rishivg/IO-SDR/Images/1.png

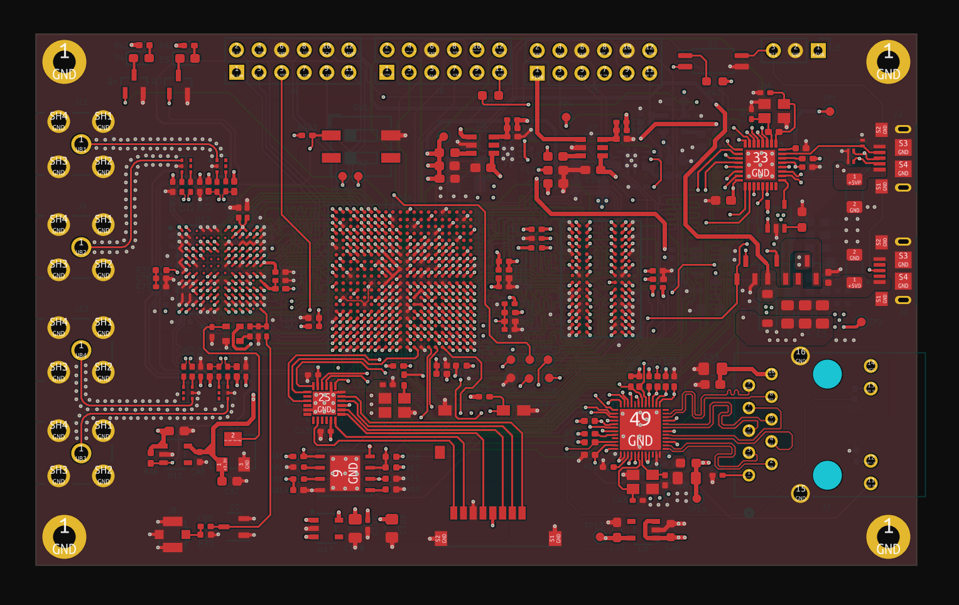
Images/1.png
