rishivg/IO-SDR/Images/2.png

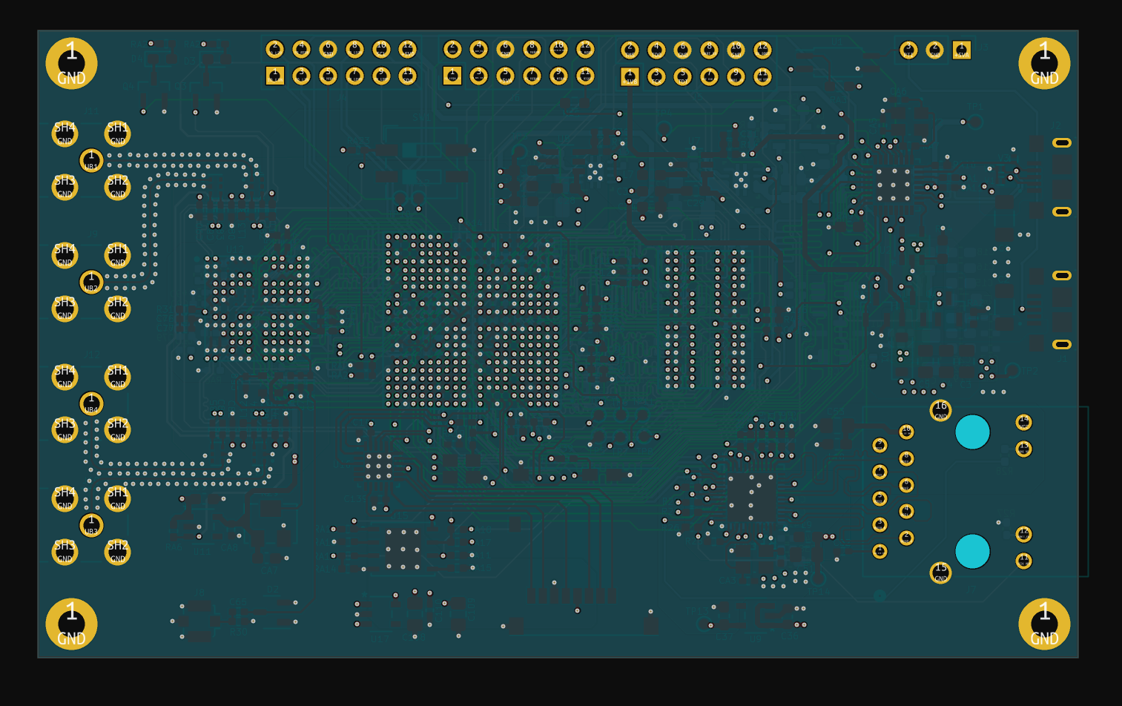
Images/2.png
