rishivg/IO-SDR/Images/3.png

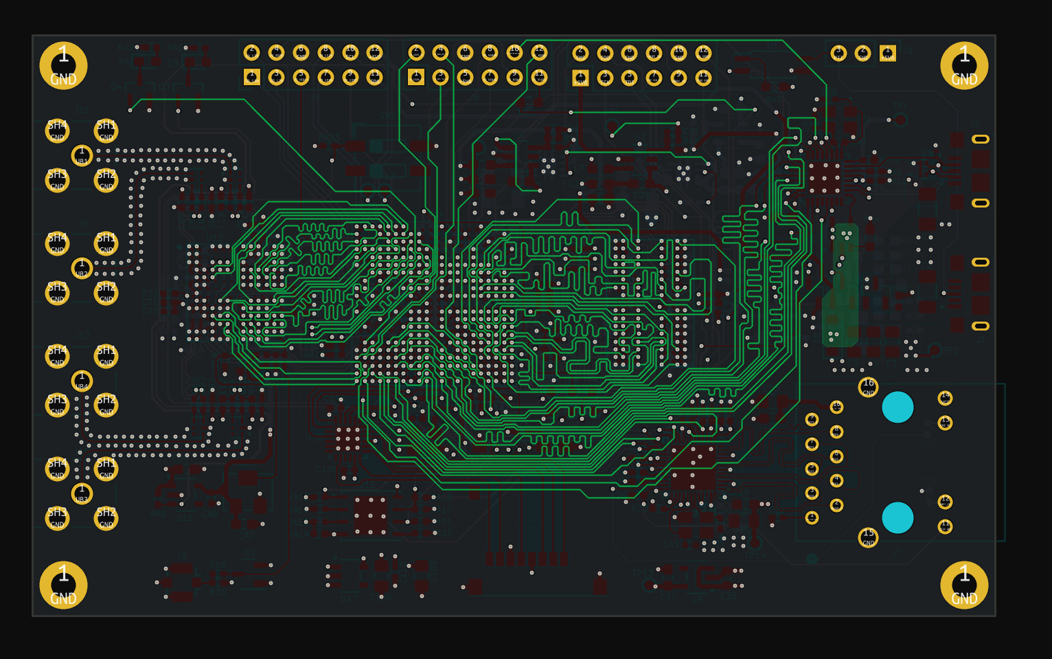
Images/3.png
