rishivg/IO-SDR/Images/4.png

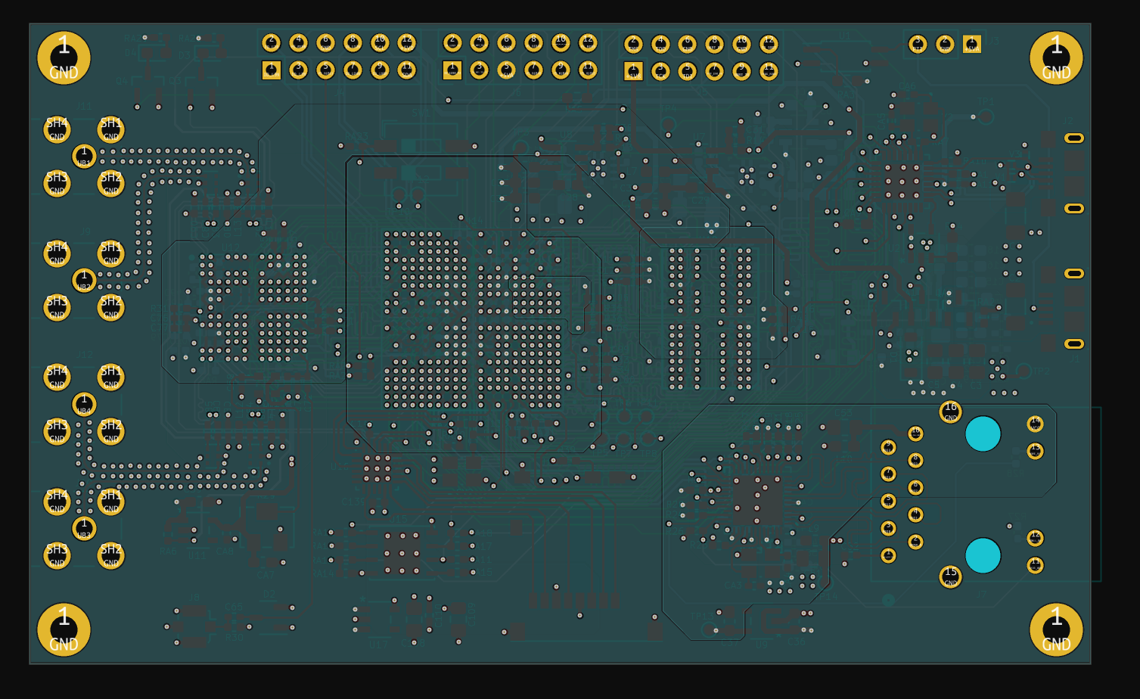
Images/4.png
