rishivg/IO-SDR/Images/5.png

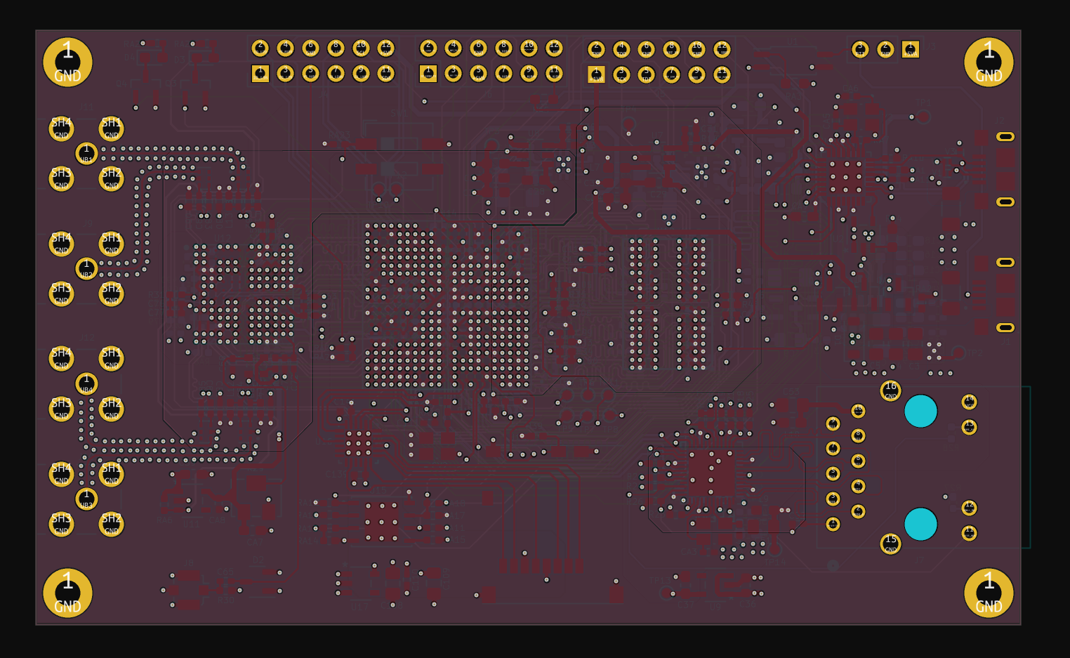
Images/5.png
