rishivg/IO-SDR/Images/6.png

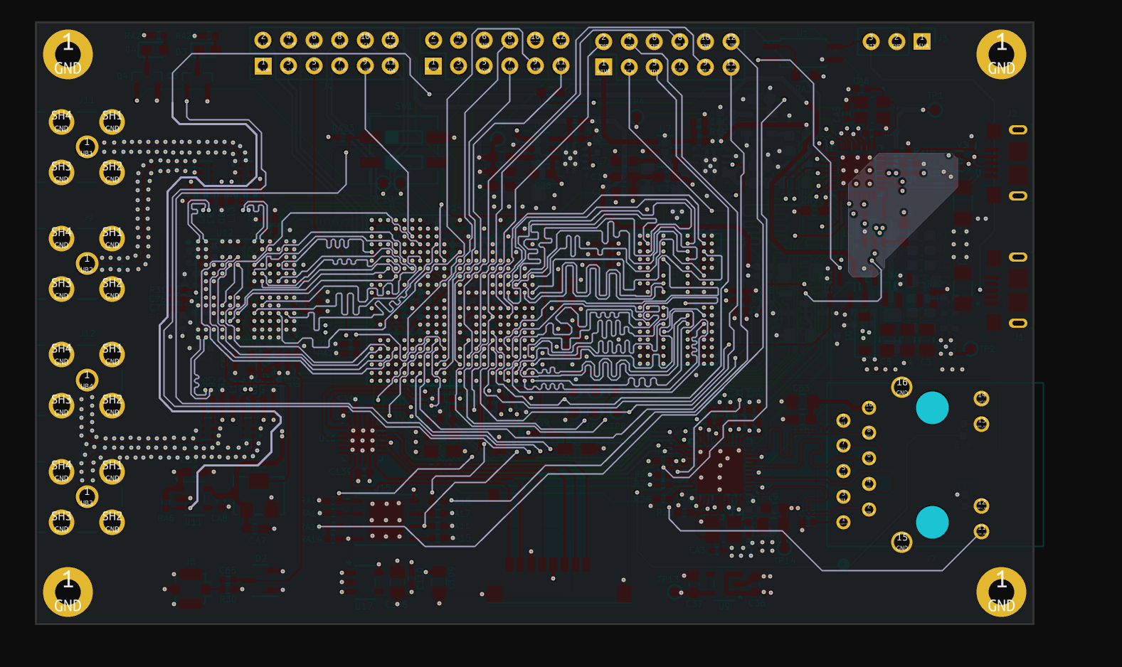
Images/6.png
