rishivg/IO-SDR/Images/7.png

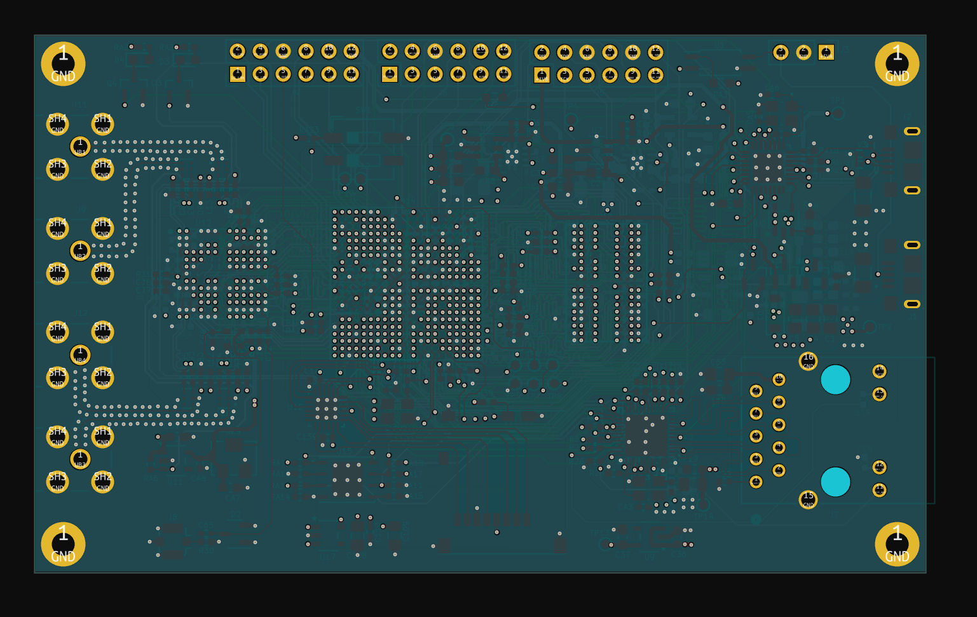
Images/7.png
