rishivg/IO-SDR/Images/8.png

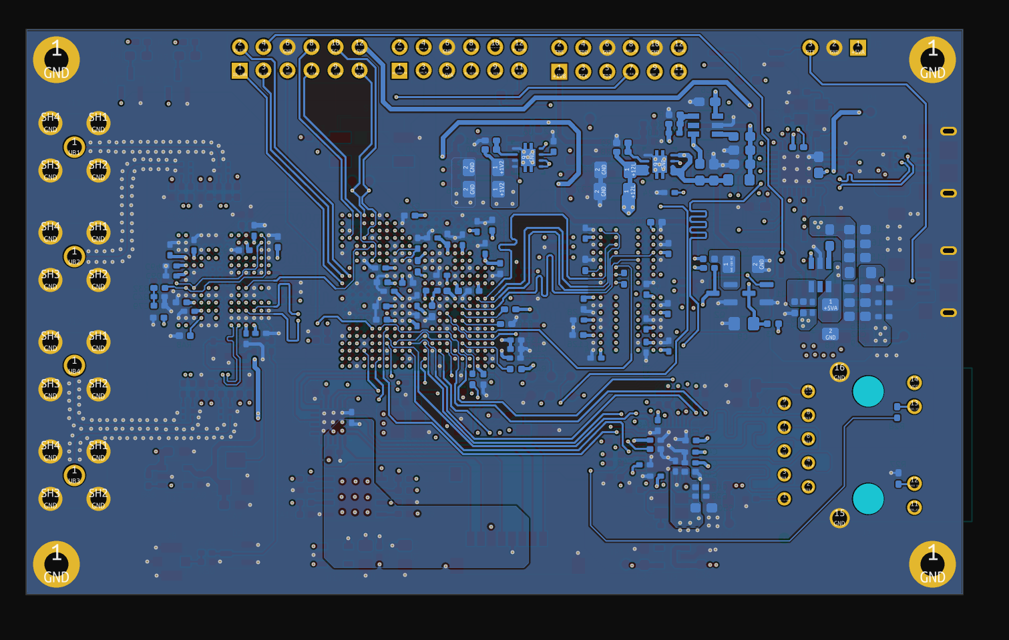
Images/8.png
